yoichiro/lunakey/pico/rev2/pcb/lunakey_pico.kicad_sch

## KiCad design pico/rev2/pcb/lunakey_pico.kicad_sch (2022-10-03)

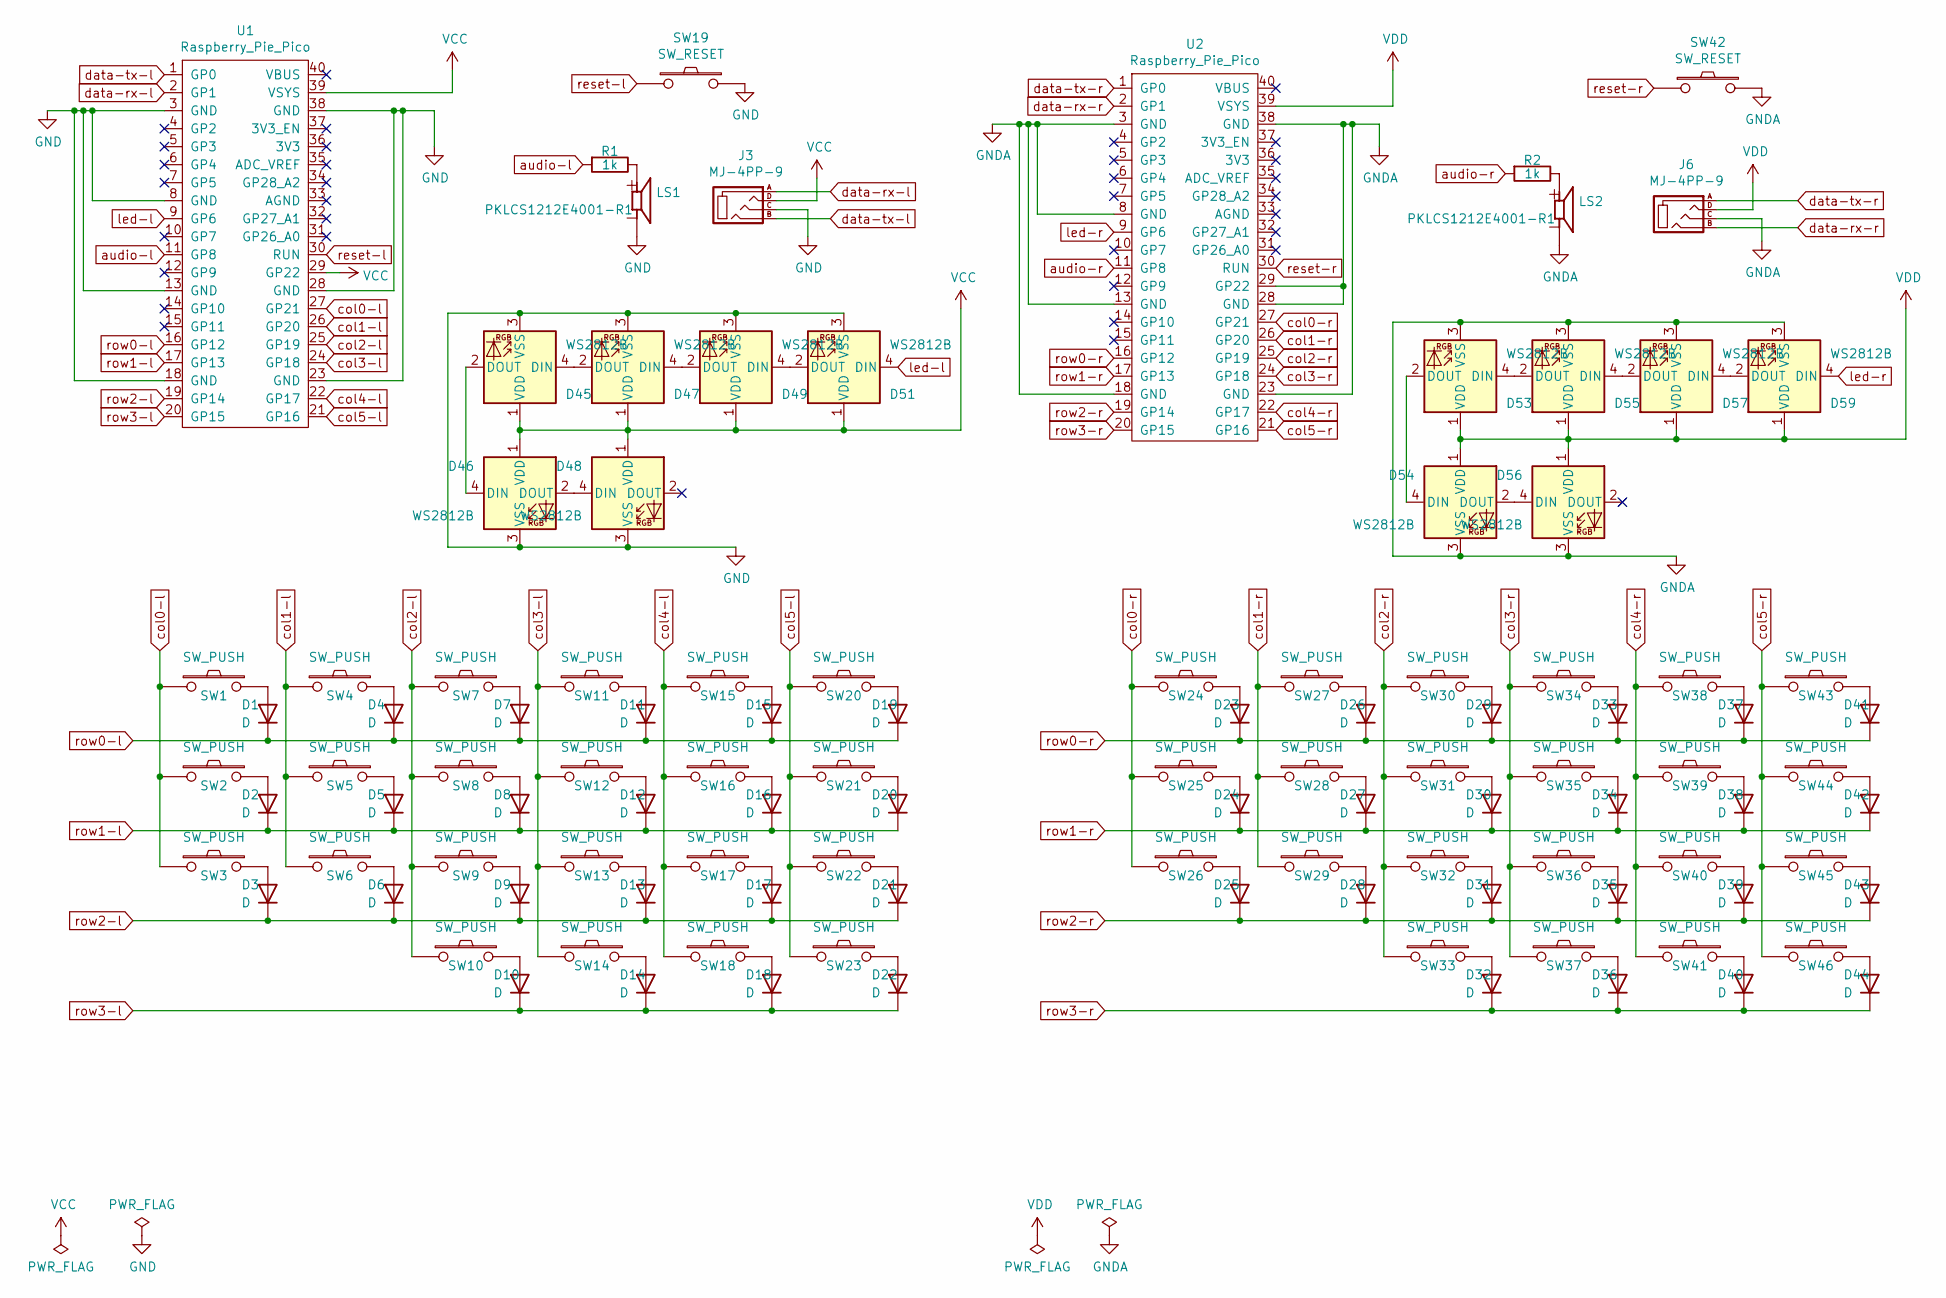
[picture p4: schematic lunakey_pico.kicad_sch]

Parts:
D1, D2, D3, D4, D5, D6, D7, D8, D9, D10, D11, D12, D13, D14, D15, D16, D17, D18, D19, D20, D21, D22, D23, D24, D25, D26, D27, D28, D29, D30, D31, D32, D33, D34, D35, D36, D37, D38, D39, D40, D41, D42, D43, D44: D; Diode-Hybrid-Back
D45, D46, D47, D48, D49, D51, D53, D54, D55, D56, D57, D59: WS2812B; LED_WS2812B
J3, J6: MJ-4PP-9; MJ-4PP-9_1side
LS1, LS2: PKLCS1212E4001-R1; SPKR_PKLCS1212E4001-R1
R1, R2: 1k; Resistor-Hybrid-Back
SW1, SW2, SW3, SW4, SW5, SW6, SW7, SW8, SW9, SW10, SW11, SW12, SW13, SW14, SW15, SW16, SW17, SW18, SW20, SW21, SW22, SW23, SW24, SW25, SW26, SW27, SW28, SW29, SW30, SW31, SW32, SW33, SW34, SW35, SW36, SW37, SW38, SW39, SW40, SW41, SW43, SW44, SW45, SW46: SW_PUSH; CherryMX_Choco_Hotswap
SW19, SW42: SW_RESET; ResetSW_1side
U1, U2: Raspberry_Pie_Pico; Raspberry_Pi_Pico

Connections:
GND: D45.3 (VSS), D46.3 (VSS), D47.3 (VSS), D48.3 (VSS), D49.3 (VSS), D51.3 (VSS), J3.C, LS1.N, SW19.2, U1.3 (GND), U1.8 (GND), U1.13 (GND), U1.18 (GND), U1.23 (GND), U1.28 (GND), U1.38 (GND)
GNDA: D53.3 (VSS), D54.3 (VSS), D55.3 (VSS), D56.3 (VSS), D57.3 (VSS), D59.3 (VSS), J6.C, LS2.N, SW42.2, U2.3 (GND), U2.8 (GND), U2.13 (GND), U2.18 (GND), U2.23 (GND), U2.28 (GND), U2.29 (GP22), U2.38 (GND)
unnamed: D1.2 (A), SW1.2
unnamed: D2.2 (A), SW2.2
unnamed: D3.2 (A), SW3.2
unnamed: D4.2 (A), SW4.2
unnamed: D5.2 (A), SW5.2
unnamed: D6.2 (A), SW6.2
unnamed: D7.2 (A), SW7.2
unnamed: D8.2 (A), SW8.2
unnamed: D9.2 (A), SW9.2
unnamed: D10.2 (A), SW10.2
unnamed: D11.2 (A), SW11.2
unnamed: D12.2 (A), SW12.2
unnamed: D13.2 (A), SW13.2
unnamed: D14.2 (A), SW14.2
unnamed: D15.2 (A), SW15.2
unnamed: D16.2 (A), SW16.2
unnamed: D17.2 (A), SW17.2
unnamed: D18.2 (A), SW18.2
unnamed: D19.2 (A), SW20.2
unnamed: D20.2 (A), SW21.2
unnamed: D21.2 (A), SW22.2
unnamed: D22.2 (A), SW23.2
unnamed: D23.2 (A), SW24.2
unnamed: D24.2 (A), SW25.2
unnamed: D25.2 (A), SW26.2
unnamed: D26.2 (A), SW27.2
unnamed: D27.2 (A), SW28.2
unnamed: D28.2 (A), SW29.2
unnamed: D29.2 (A), SW30.2
unnamed: D30.2 (A), SW31.2
unnamed: D31.2 (A), SW32.2
unnamed: D32.2 (A), SW33.2
unnamed: D33.2 (A), SW34.2
unnamed: D34.2 (A), SW35.2
unnamed: D35.2 (A), SW36.2
unnamed: D36.2 (A), SW37.2
unnamed: D37.2 (A), SW38.2
unnamed: D38.2 (A), SW39.2
unnamed: D39.2 (A), SW40.2
unnamed: D40.2 (A), SW41.2
unnamed: D41.2 (A), SW43.2
unnamed: D42.2 (A), SW44.2
unnamed: D43.2 (A), SW45.2
unnamed: D44.2 (A), SW46.2
unnamed: D45.2 (DOUT), D46.4 (DIN)
unnamed: D45.4 (DIN), D47.2 (DOUT)
unnamed: D46.2 (DOUT), D48.4 (DIN)
unnamed: D47.4 (DIN), D49.2 (DOUT)
unnamed: D49.4 (DIN), D51.2 (DOUT)
unnamed: D53.2 (DOUT), D54.4 (DIN)
unnamed: D53.4 (DIN), D55.2 (DOUT)
unnamed: D54.2 (DOUT), D56.4 (DIN)
unnamed: D55.4 (DIN), D57.2 (DOUT)
unnamed: D57.4 (DIN), D59.2 (DOUT)
unnamed: LS1.P, R1.1
unnamed: LS2.P, R2.1
VCC: D45.1 (VDD), D46.1 (VDD), D47.1 (VDD), D48.1 (VDD), D49.1 (VDD), D51.1 (VDD), J3.D, U1.39 (VSYS)
VDD: D53.1 (VDD), D54.1 (VDD), D55.1 (VDD), D56.1 (VDD), D57.1 (VDD), D59.1 (VDD), J6.D, U2.39 (VSYS)
audio-l: R1.2, U1.11 (GP8)
audio-r: R2.2, U2.11 (GP8)
col0-l: SW1.1, SW2.1, SW3.1, U1.27 (GP21)
col0-r: SW24.1, SW25.1, SW26.1, U2.27 (GP21)
col1-l: SW4.1, SW5.1, SW6.1, U1.26 (GP20)
col1-r: SW27.1, SW28.1, SW29.1, U2.26 (GP20)
col2-l: SW7.1, SW8.1, SW9.1, SW10.1, U1.25 (GP19)
col2-r: SW30.1, SW31.1, SW32.1, SW33.1, U2.25 (GP19)
col3-l: SW11.1, SW12.1, SW13.1, SW14.1, U1.24 (GP18)
col3-r: SW34.1, SW35.1, SW36.1, SW37.1, U2.24 (GP18)
col4-l: SW15.1, SW16.1, SW17.1, SW18.1, U1.22 (GP17)
col4-r: SW38.1, SW39.1, SW40.1, SW41.1, U2.22 (GP17)
col5-l: SW20.1, SW21.1, SW22.1, SW23.1, U1.21 (GP16)
col5-r: SW43.1, SW44.1, SW45.1, SW46.1, U2.21 (GP16)
data-rx-l: J3.A, U1.2 (GP1)
data-rx-r: J6.B, U2.2 (GP1)
data-tx-l: J3.B, U1.1 (GP0)
data-tx-r: J6.A, U2.1 (GP0)
led-l: D51.4 (DIN), U1.9 (GP6)
led-r: D59.4 (DIN), U2.9 (GP6)
reset-l: SW19.1, U1.30 (RUN)
reset-r: SW42.1, U2.30 (RUN)
row0-l: D1.1 (K), D4.1 (K), D7.1 (K), D11.1 (K), D15.1 (K), D19.1 (K), U1.16 (GP12)
row0-r: D23.1 (K), D26.1 (K), D29.1 (K), D33.1 (K), D37.1 (K), D41.1 (K), U2.16 (GP12)
row1-l: D2.1 (K), D5.1 (K), D8.1 (K), D12.1 (K), D16.1 (K), D20.1 (K), U1.17 (GP13)
row1-r: D24.1 (K), D27.1 (K), D30.1 (K), D34.1 (K), D38.1 (K), D42.1 (K), U2.17 (GP13)
row2-l: D3.1 (K), D6.1 (K), D9.1 (K), D13.1 (K), D17.1 (K), D21.1 (K), U1.19 (GP14)
row2-r: D25.1 (K), D28.1 (K), D31.1 (K), D35.1 (K), D39.1 (K), D43.1 (K), U2.19 (GP14)
row3-l: D10.1 (K), D14.1 (K), D18.1 (K), D22.1 (K), U1.20 (GP15)
row3-r: D32.1 (K), D36.1 (K), D40.1 (K), D44.1 (K), U2.20 (GP15)
